Amp-Lab-at-VT/Stylophone/Stylophone Circuit/PUT/Stylophone_with_battery_2.png

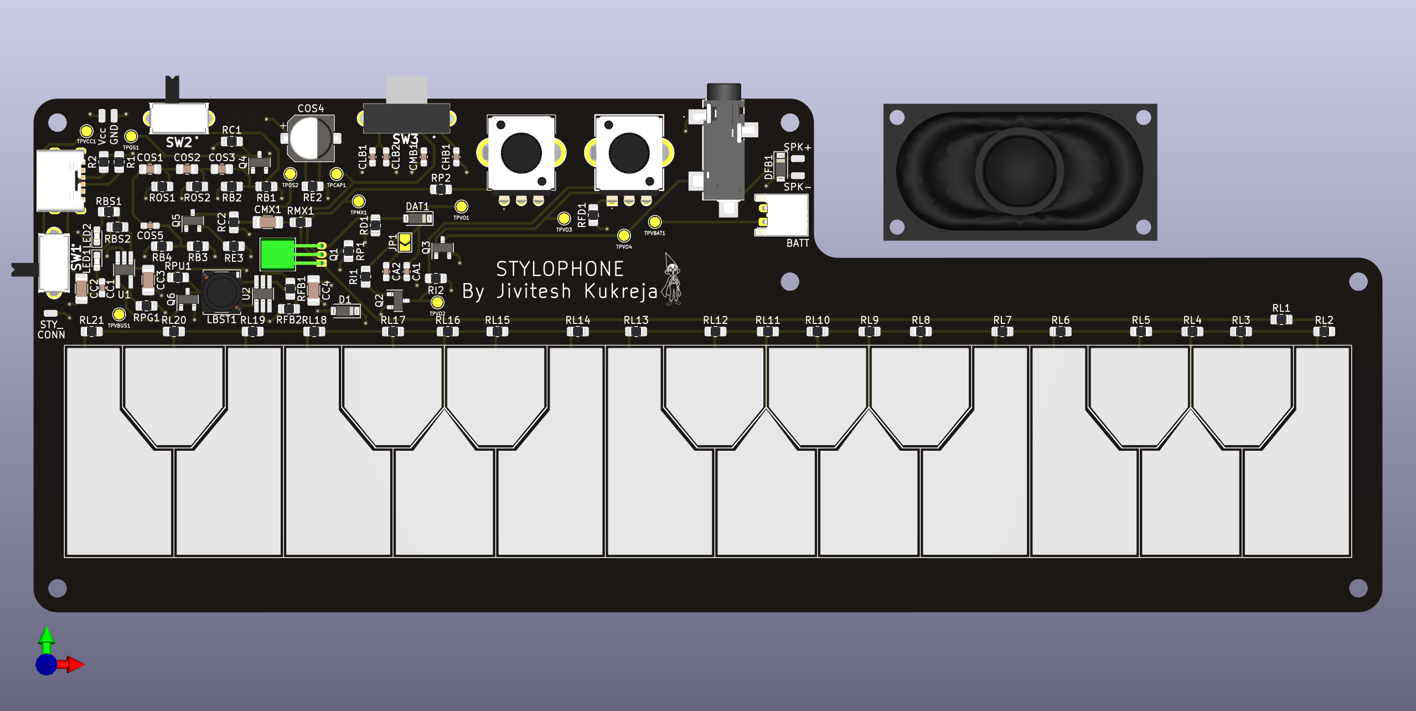
Stylophone Circuit/PUT/Stylophone_with_battery_2.png
